alexmrqt/Philips-GAM-48-303-daughterboard/docs/DSC_6184.JPG

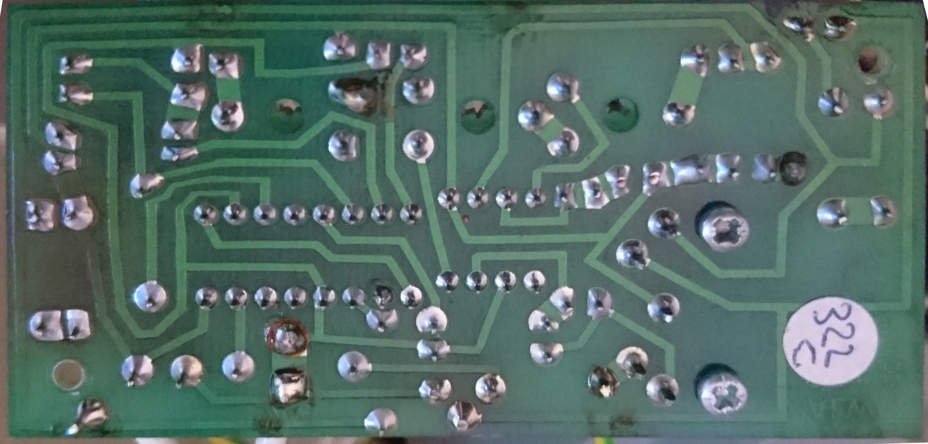
docs/DSC_6184.JPG
